snorklerjoe/breadboard-vna/hardware/SuperVNA/SuperVNA.kicad_sch

## KiCad design hardware/SuperVNA/SuperVNA.kicad_sch (2025-12-09, an earlier design)

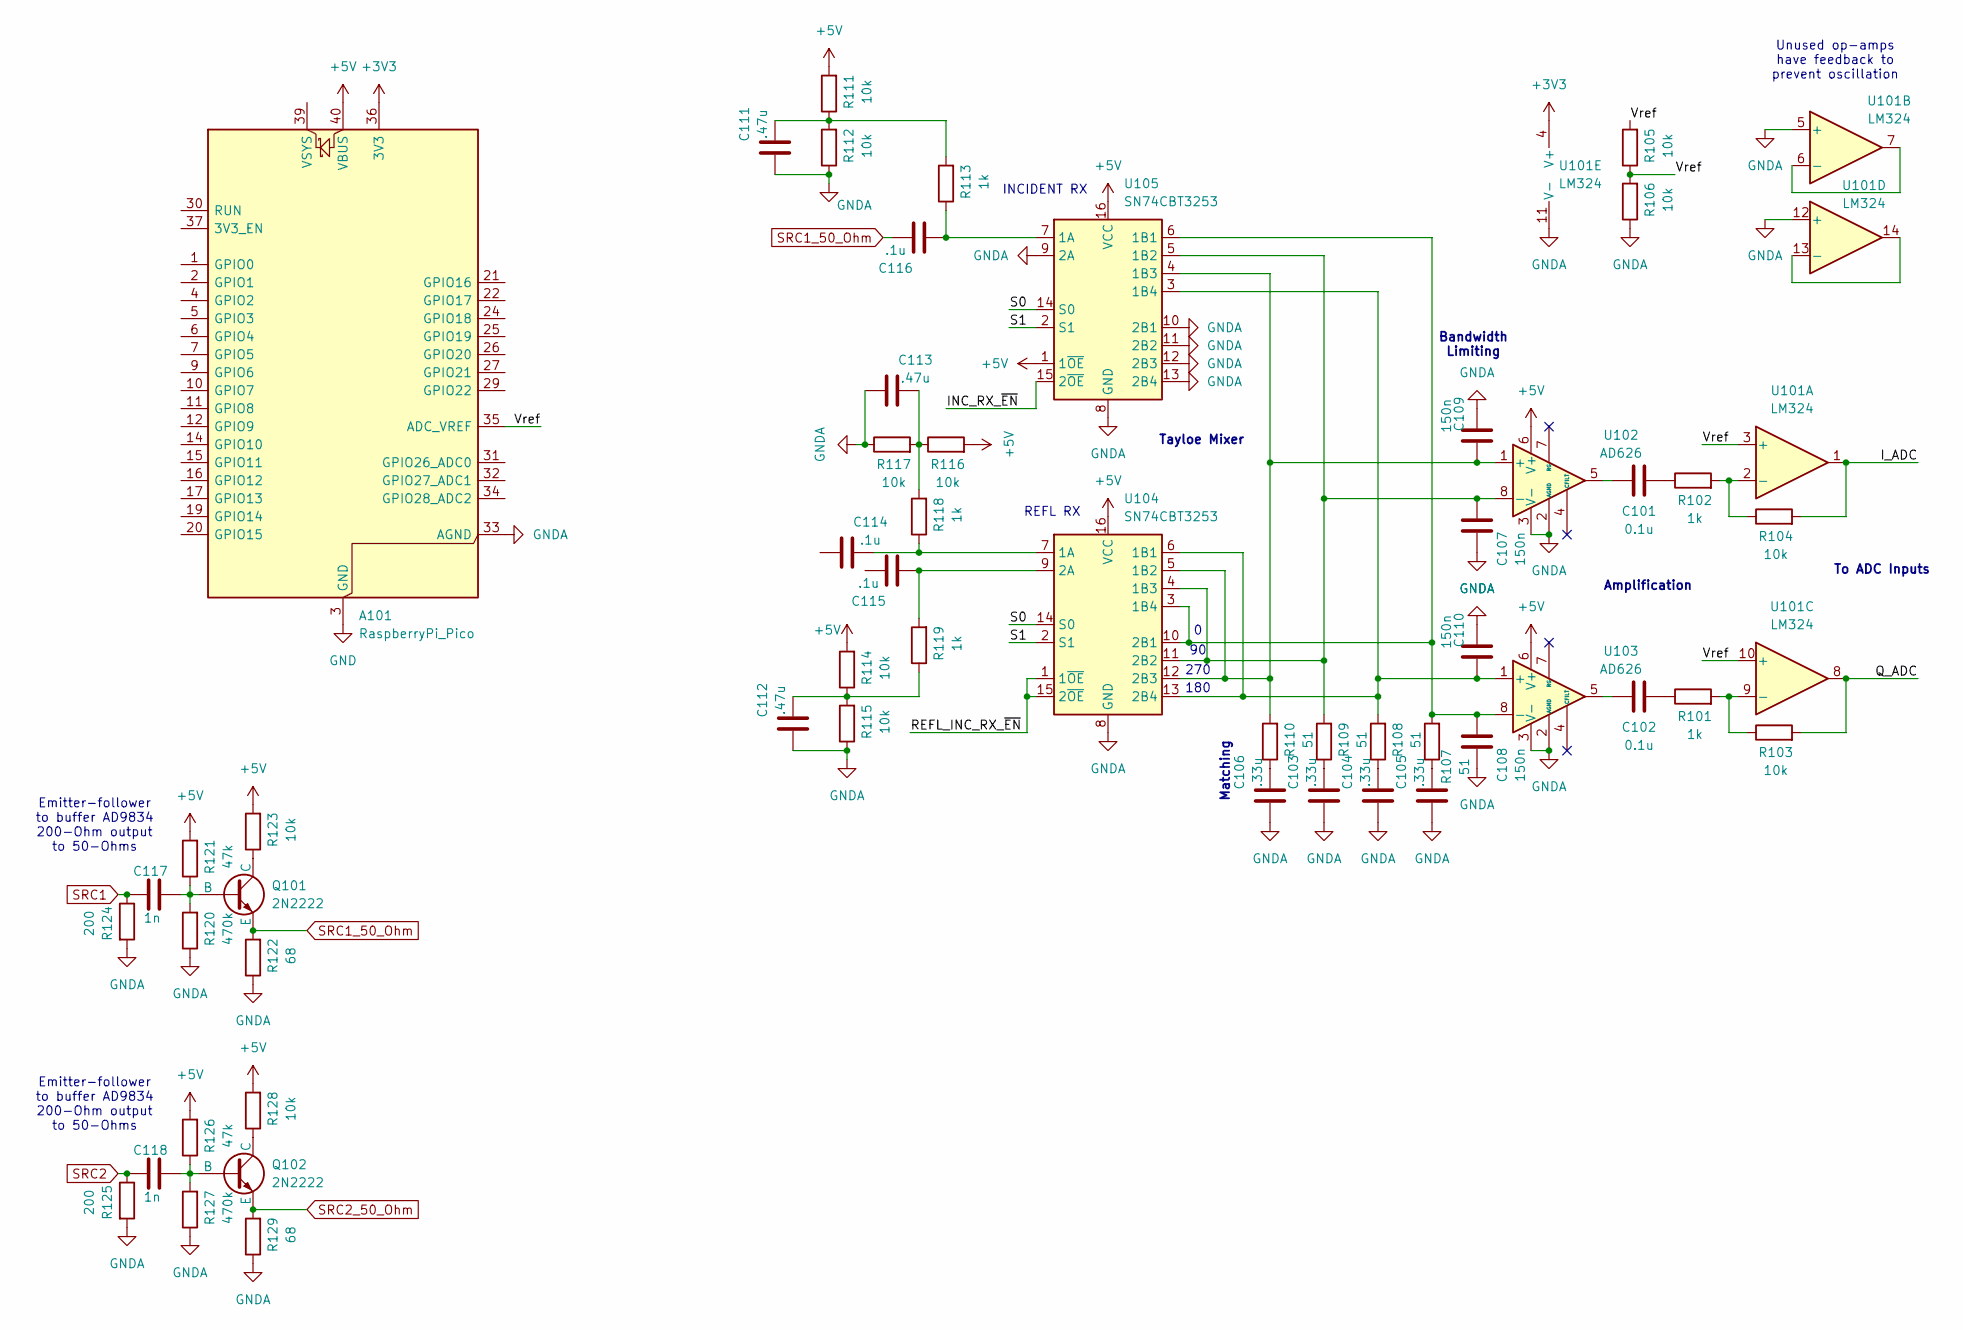
[picture p6: schematic SuperVNA.kicad_sch]

Parts:
A101: RaspberryPi_Pico; RaspberryPi_Pico_Common_Unspecified
C101, C102: 0.1u
C103, C104, C105, C106: .33u
C107, C108, C109, C110: 150n
C111, C112, C113: .47u
C114, C115, C116: .1u
C117, C118: 1n
Q101, Q102: 2N2222
R101, R102, R113, R118, R119: 1k
R103, R104, R105, R106, R111, R112, R114, R115, R116, R117, R123, R128: 10k
R107, R108, R109, R110: 51
R120, R127: 470k
R121, R126: 47k
R122, R129: 68
R124, R125: 200
U101: LM324
U102, U103: AD626
U104, U105: SN74CBT3253

Connections:
+3V3: A101.36 (3V3), U101.4 (V+)
+5V: A101.40 (VBUS), R111.2, R114.2, R116.2, R121.2, R123.2, R126.2, R128.2, U102.6 (V+), U103.6 (V+), U104.16 (VCC), U105.1 (1~OE), U105.16 (VCC)
GND: A101.3 (GND), A101.8 (GND), A101.13 (GND), A101.18 (GND), A101.23 (GND), A101.28 (GND), A101.38 (GND)
GNDA: A101.33 (AGND), C103.2, C104.2, C105.2, C106.2, C107.2, C108.2, C109.2, C110.2, C111.2, C112.2, C113.2, R106.1, R112.1, R115.1, R117.1, R120.1, R122.1, R124.2, R125.2, R127.1, R129.1, U101.5 (+), U101.11 (V-), U101.12 (+), U102.2 (AGND), U102.3 (V-), U103.2 (AGND), U103.3 (V-), U104.8 (GND), U105.8 (GND), U105.9 (2A), U105.10 (2B1), U105.11 (2B2), U105.12 (2B3), U105.13 (2B4)
INC_RX_~EN: U105.15 (2~OE)
I_ADC: R104.2, U101.1
unnamed: C101.1, R102.1
unnamed: C101.2, U102.5
unnamed: C102.1, R101.1
unnamed: C102.2, U103.5
unnamed: C103.1, R109.1
unnamed: C104.1, R108.1
unnamed: C105.1, R107.1
unnamed: C106.1, R110.1
unnamed: C107.1, R109.2, U102.8 (-), U104.4 (1B3), U104.11 (2B2), U105.5 (1B2)
unnamed: C108.1, R107.2, U103.8 (-), U104.3 (1B4), U104.10 (2B1), U105.6 (1B1)
unnamed: C109.1, R110.2, U102.1 (+), U104.5 (1B2), U104.12 (2B3), U105.4 (1B3)
unnamed: C110.1, R108.2, U103.1 (+), U104.6 (1B1), U104.13 (2B4), U105.3 (1B4)
unnamed: C111.1, R111.1, R112.2, R113.2
unnamed: C112.1, R114.1, R115.2, R119.1
unnamed: C113.1, R116.1, R117.2, R118.2
unnamed: C114.1, R118.1, U104.7 (1A)
unnamed: C115.2, R119.2, U104.9 (2A)
unnamed: C116.2, R113.1, U105.7 (1A)
unnamed: C117.2, Q101.2 (B), R120.2, R121.1
unnamed: C118.2, Q102.2 (B), R126.1, R127.2
unnamed: Q101.1 (C), R123.1
unnamed: Q102.1 (C), R128.1
unnamed: R101.2, R103.1, U101.9 (-)
unnamed: R102.2, R104.1, U101.2 (-)
unnamed: U101.6 (-), U101.7
unnamed: U101.13 (-), U101.14
Q_ADC: R103.2, U101.8
REFL_INC_RX_~EN: U104.1 (1~OE), U104.15 (2~OE)
S0: U104.14 (S0), U105.14 (S0)
S1: U104.2 (S1), U105.2 (S1)
SRC1: C117.1, R124.1
SRC1_50_Ohm: C116.1, Q101.3 (E), R122.2
SRC2: C118.1, R125.1
SRC2_50_Ohm: Q102.3 (E), R129.2
Vref: A101.35 (ADC_VREF), R105.1, R105.2, R106.2, U101.3 (+), U101.10 (+)

Notes on the sheet:
Unused op-amps have feedback to prevent oscillation
Matching
Bandwidth Limiting
REFL RX
INCIDENT RX
To ADC Inputs
270
Emitter-follower to buffer AD9834 200-Ohm output to 50-Ohms
Amplification
Tayloe Mixer
180
